Joseph-Rance/Com-Soc-robotic-arm/object detection/classified images/1/input image.jpg

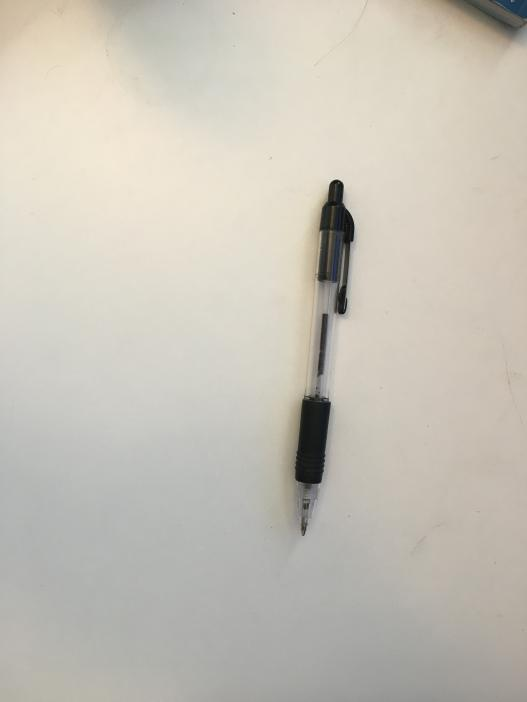
object detection/classified images/1/input image.jpg
