Joseph-Rance/Com-Soc-robotic-arm/object detection/classified images/2/input backgroud.jpg

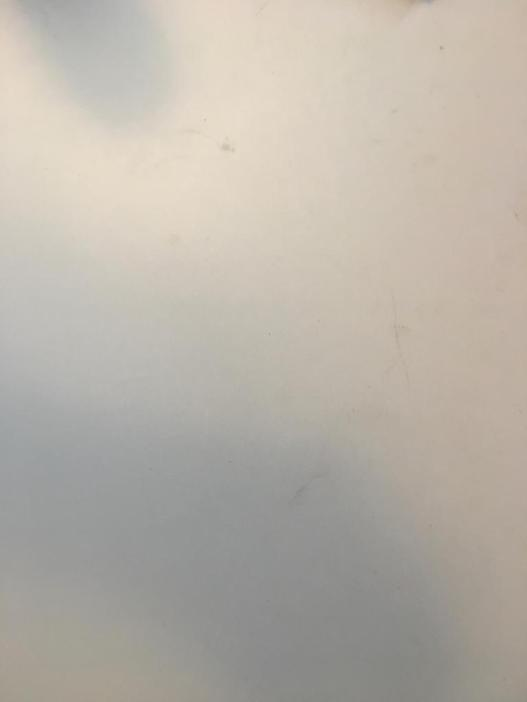
object detection/classified images/2/input backgroud.jpg
