Joseph-Rance/Com-Soc-robotic-arm/object detection/classified images/3/input background.jpg

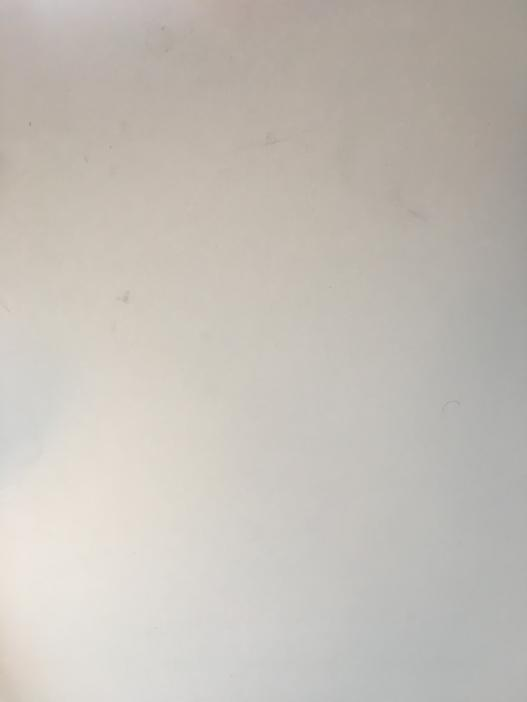
object detection/classified images/3/input background.jpg
