Joseph-Rance/Com-Soc-robotic-arm/object detection/classified images/4/input background.jpg

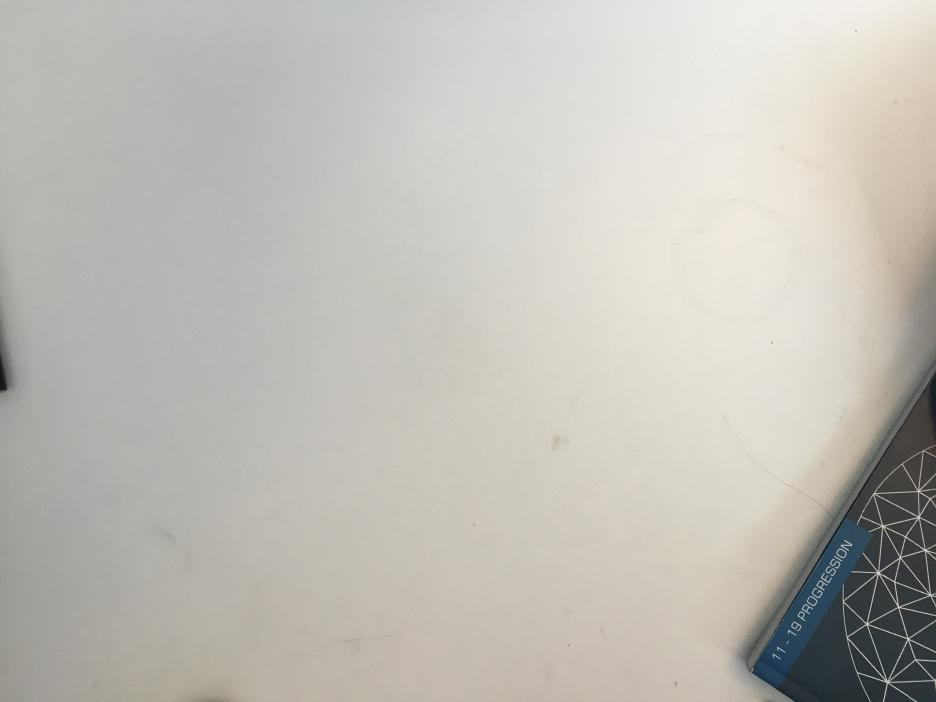
object detection/classified images/4/input background.jpg
