Joseph-Rance/Com-Soc-robotic-arm/object detection/classified images/4/output.png

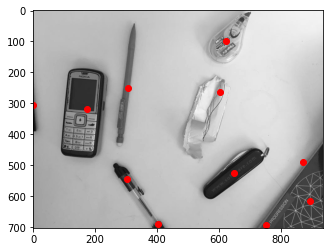
object detection/classified images/4/output.png
