Joseph-Rance/Com-Soc-robotic-arm/other engineering/printed parts.jpg

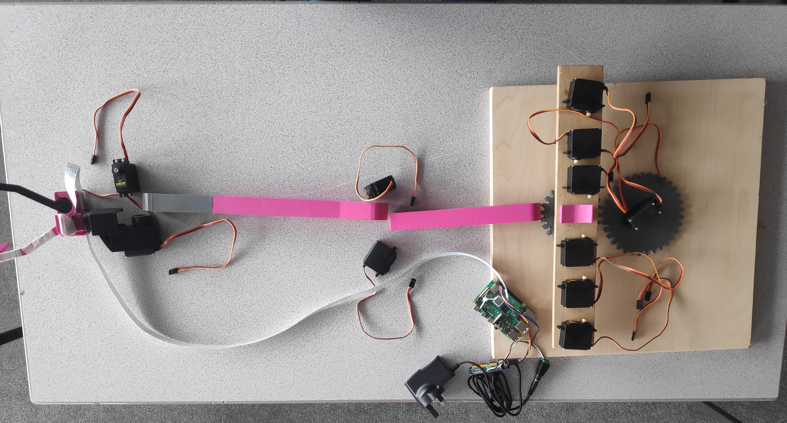
other engineering/printed parts.jpg
