Joseph-Rance/Com-Soc-robotic-arm/other engineering/assembled arm.jpg

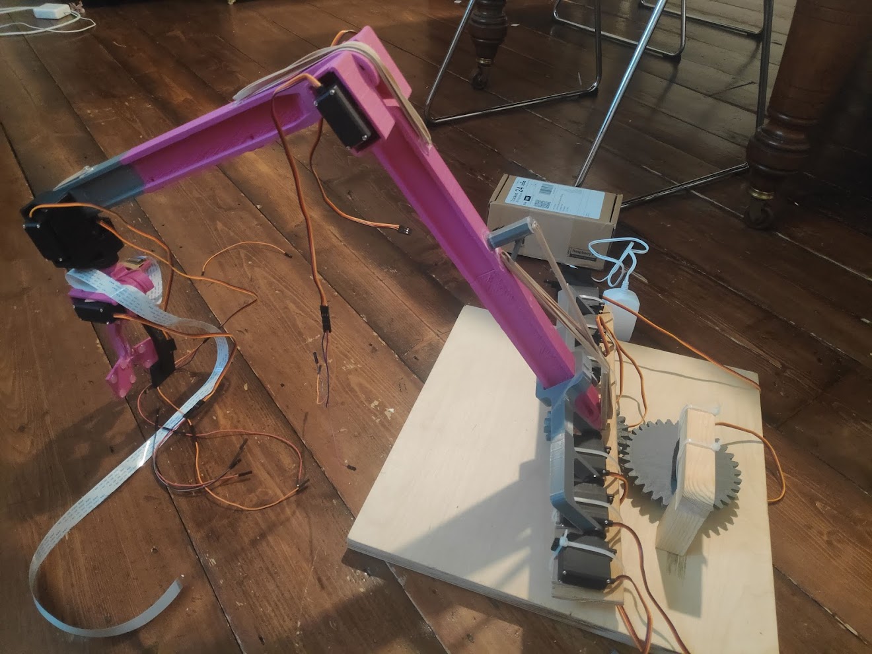
other engineering/assembled arm.jpg
